analoghifi/Thel-Black-Pulsar-PowerSupply/docs/version 2019-now/BLP10.png

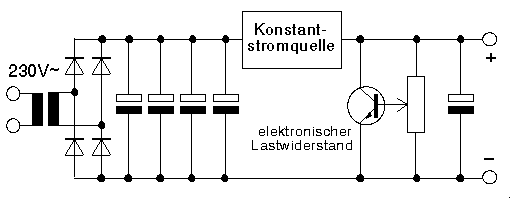
docs/version 2019-now/BLP10.png
