analoghifi/Thel-Black-Pulsar-PowerSupply/hardware/version 2013-2018/black_pulsar_2013-2018_2.jpg

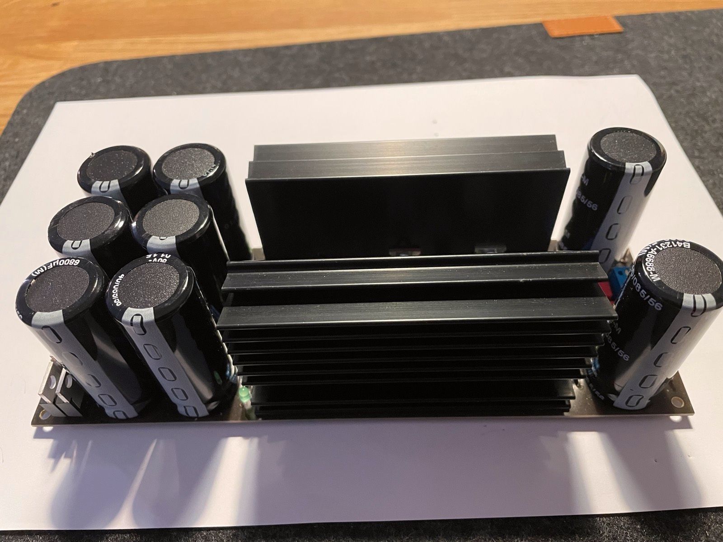
hardware/version 2013-2018/black_pulsar_2013-2018_2.jpg
