analoghifi/Thel-Black-Pulsar-PowerSupply/hardware/version 2013-2018/BLP-2.jpg

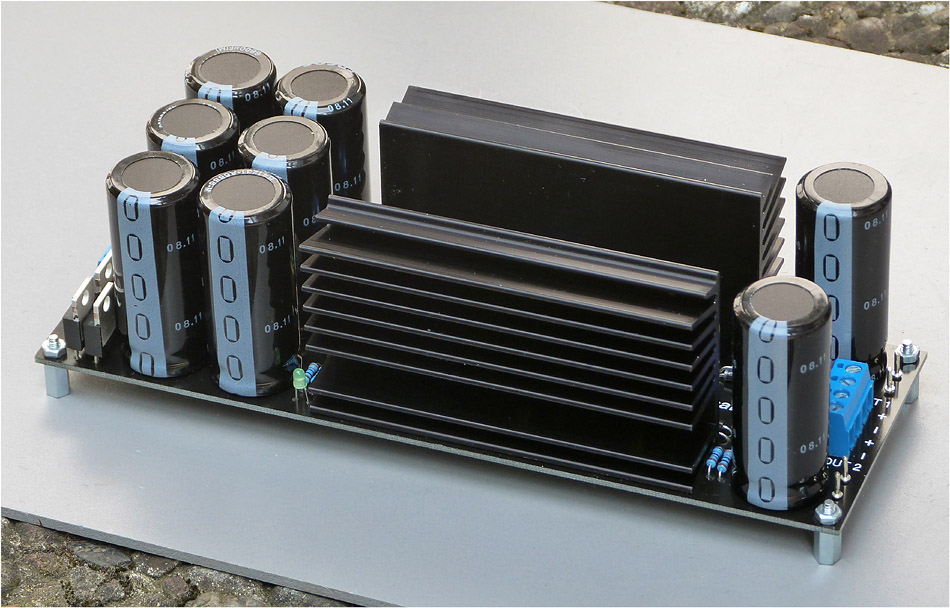
hardware/version 2013-2018/BLP-2.jpg
