analoghifi/Thel-Black-Pulsar-PowerSupply/hardware/version 2013-2018/KiCad/original/black_pulsar_2013-18_original_1Layer_THT.sch.png

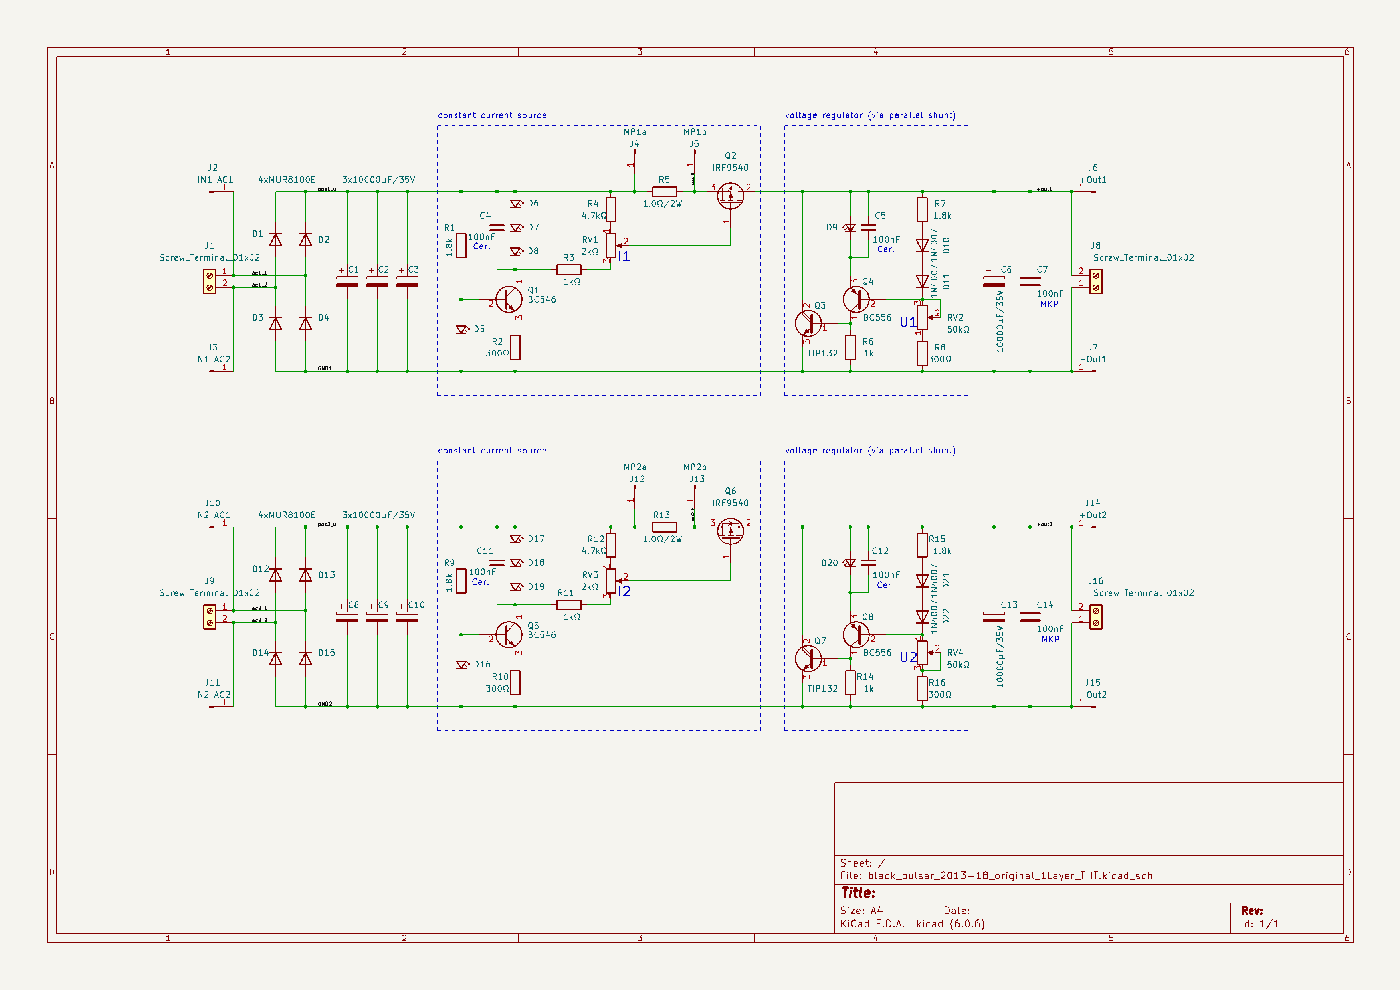
hardware/version 2013-2018/KiCad/original/black_pulsar_2013-18_original_1Layer_THT.sch.png
