analoghifi/Thel-Black-Pulsar-PowerSupply/docs/version 2013-2018/manual_black_pulsar_2013-2018_german.png

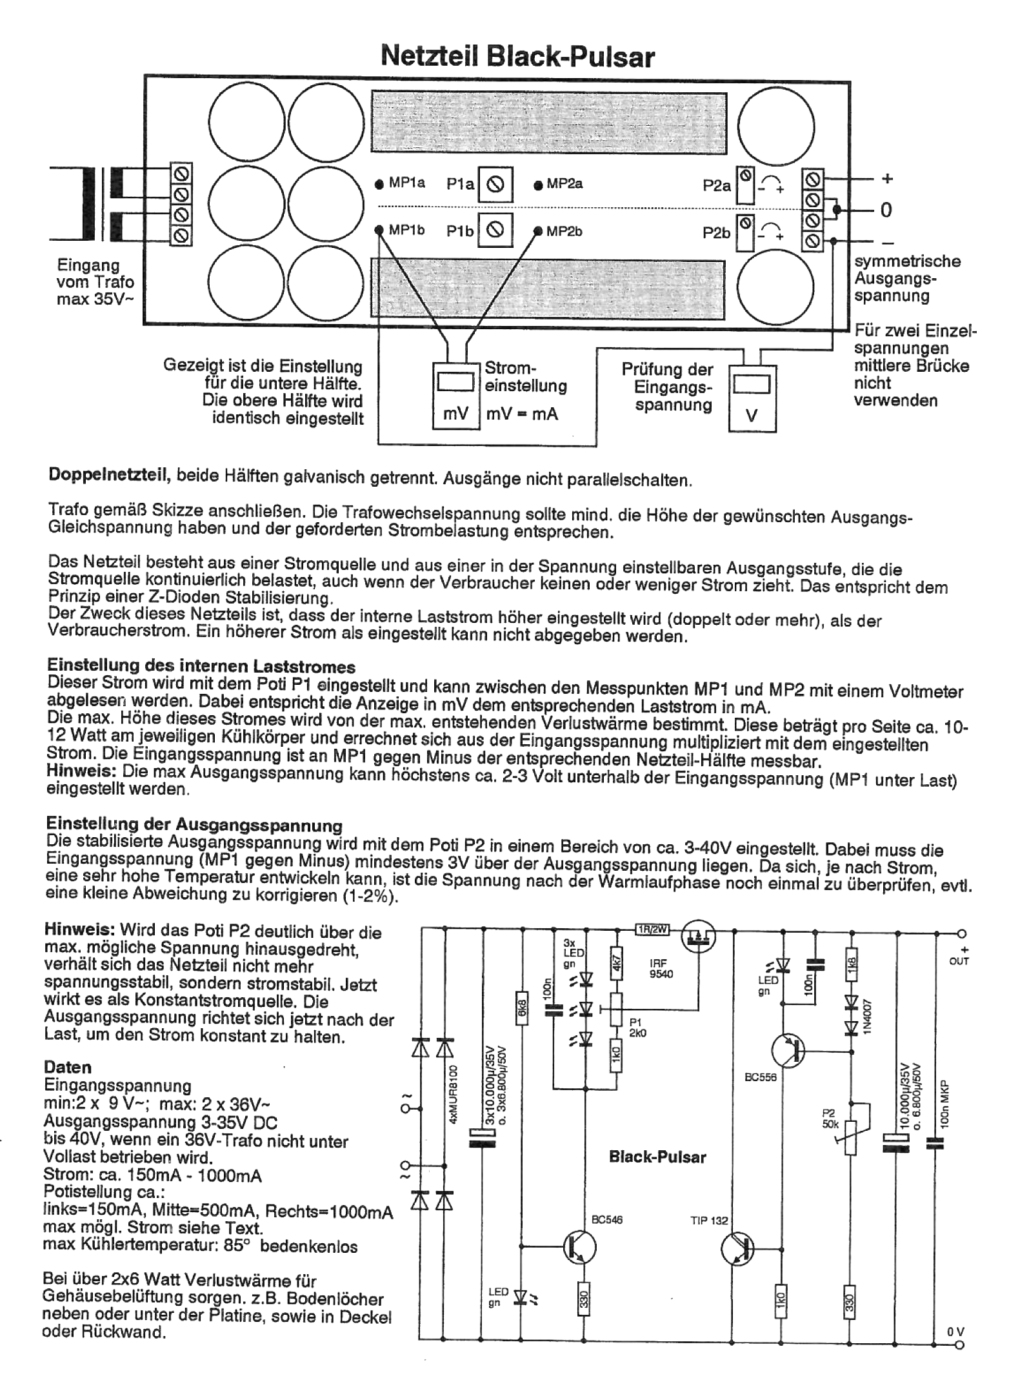
docs/version 2013-2018/manual_black_pulsar_2013-2018_german.png
