analoghifi/Thel-Black-Pulsar-PowerSupply/docs/version 2019-now/manual_german.png

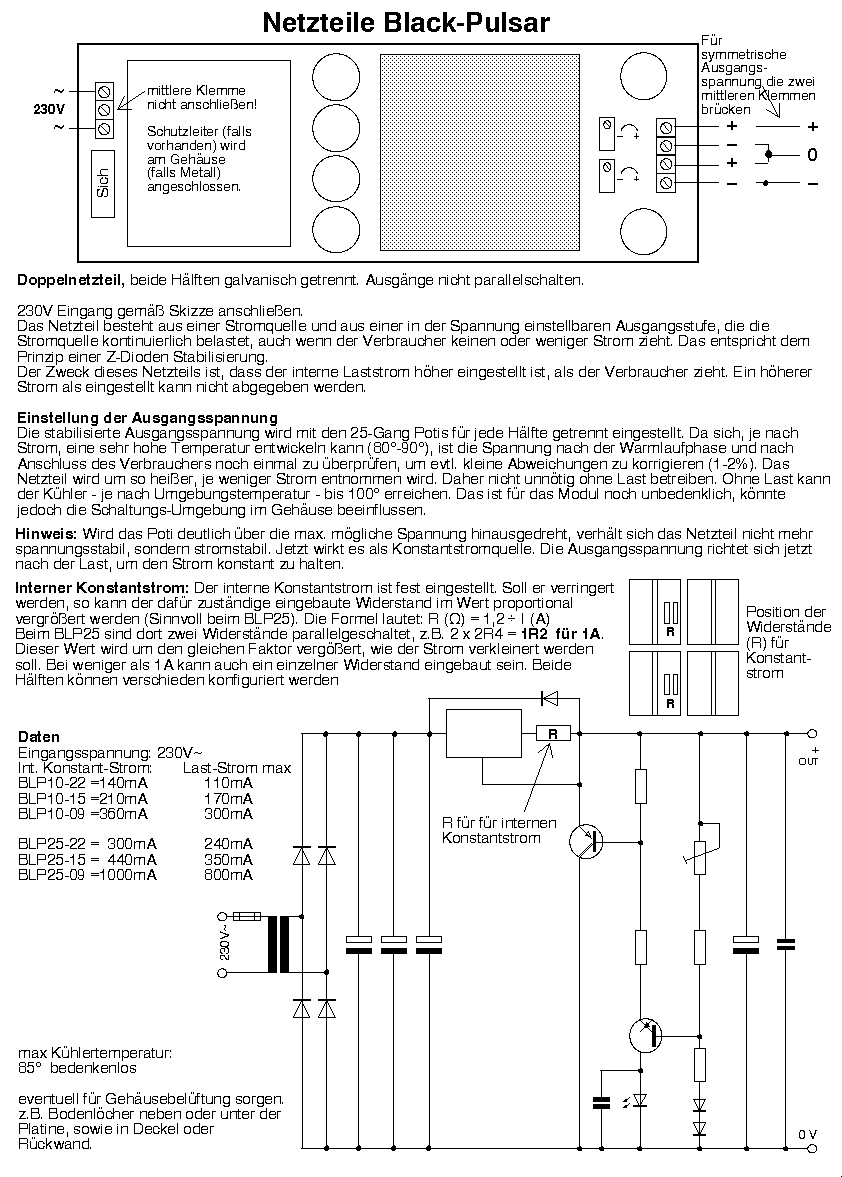
docs/version 2019-now/manual_german.png
