analoghifi/Thel-Black-Pulsar-PowerSupply/hardware/version 2013-2018/Black_pulsar_2013-2018_top_photomontage.jpg

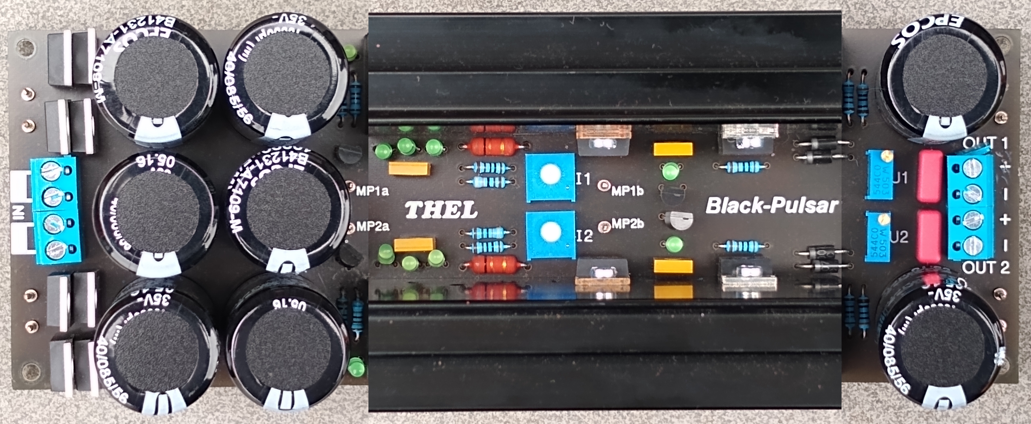
hardware/version 2013-2018/Black_pulsar_2013-2018_top_photomontage.jpg
